Doug-Wyman/ESP8266_MQTT_light/status.py

{
  "rgb": {
    "brightness": 1023,
    "brightness_scale": 1024,
    "color": {
      "r": 1023,
      "g": 0,
      "b": 200
    },
    "state": "ON",
    "transition": 2
  },
  "white": {
    "brightness": 1023,
    "brightness_scale": 1024,
    "state": "ON",
    "transition": 2
  }
}
